lpcia/Parade-Player/Media/40-8Loco_Before.png

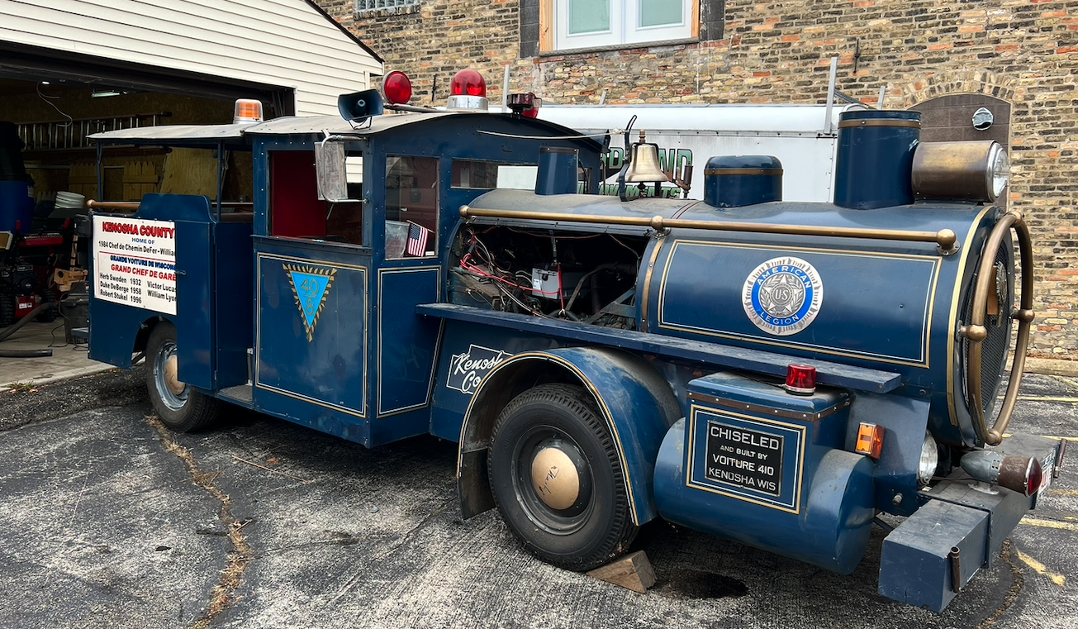
Media/40-8Loco_Before.png
