lpcia/Parade-Player/Media/Cab_Before.png

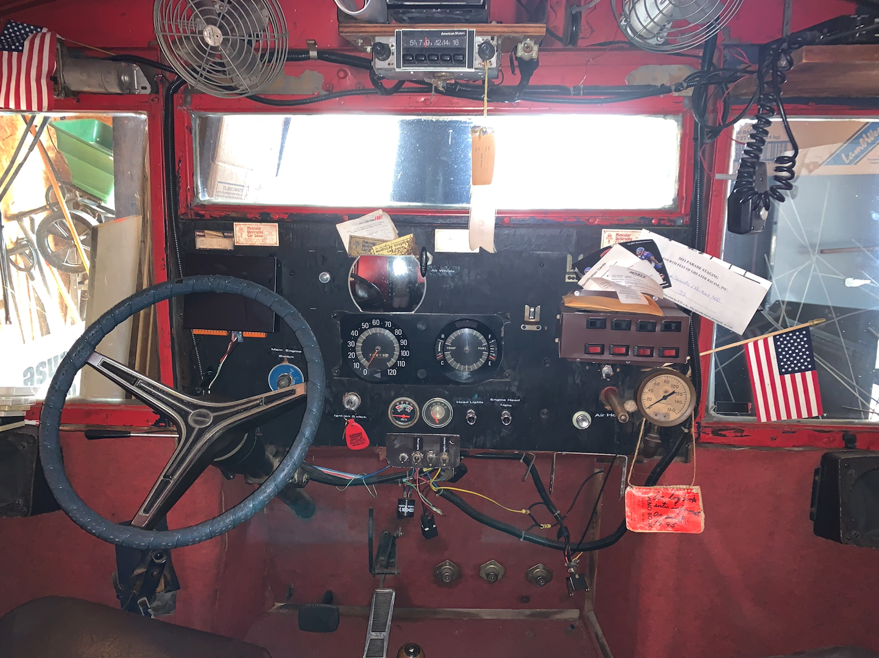
Media/Cab_Before.png
